lyso1/LCK75r2/LCK75 images/mainboard.png

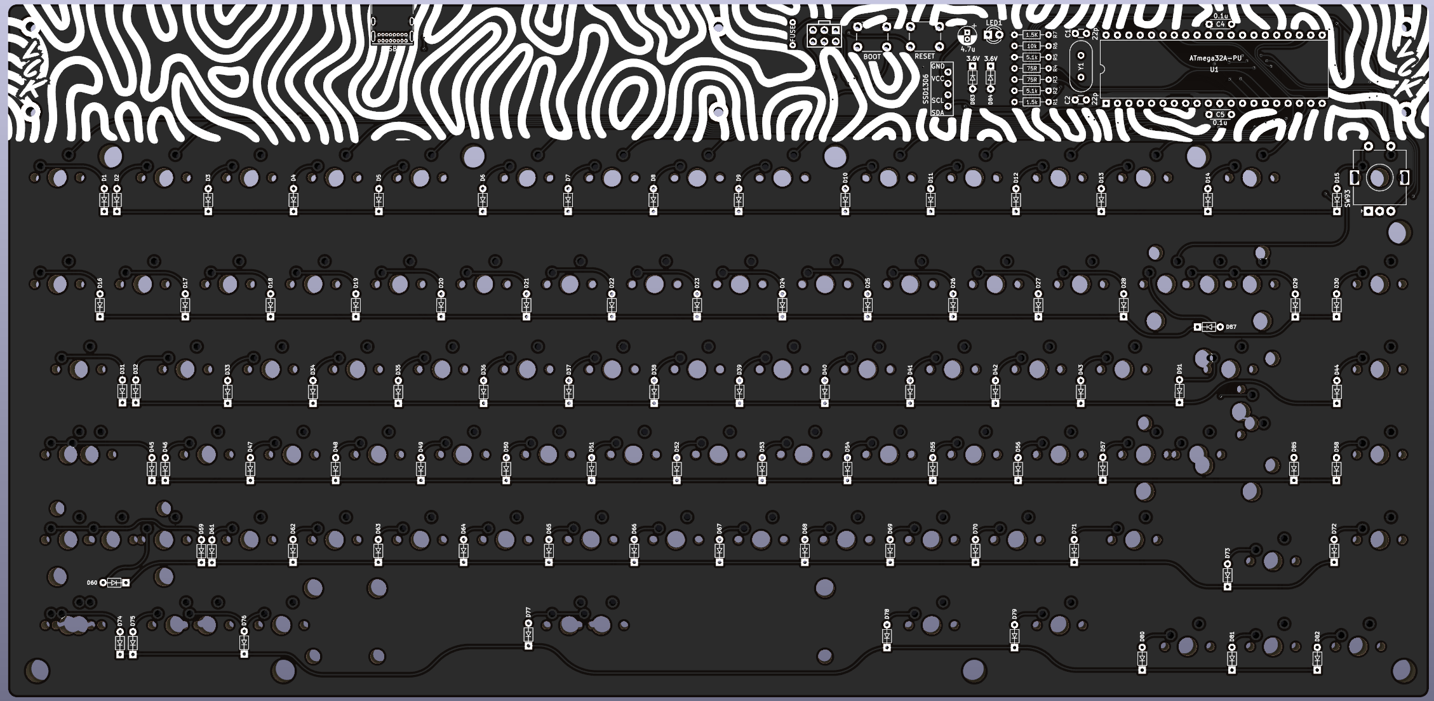
LCK75 images/mainboard.png
