lyso1/LCK75r2/LCK75gerbers&parts/LCK75r2-MAINBOARD/LCK75.kicad_sch

## KiCad design LCK75gerbers&parts/LCK75r2-MAINBOARD/LCK75.kicad_sch (2022-02-10)

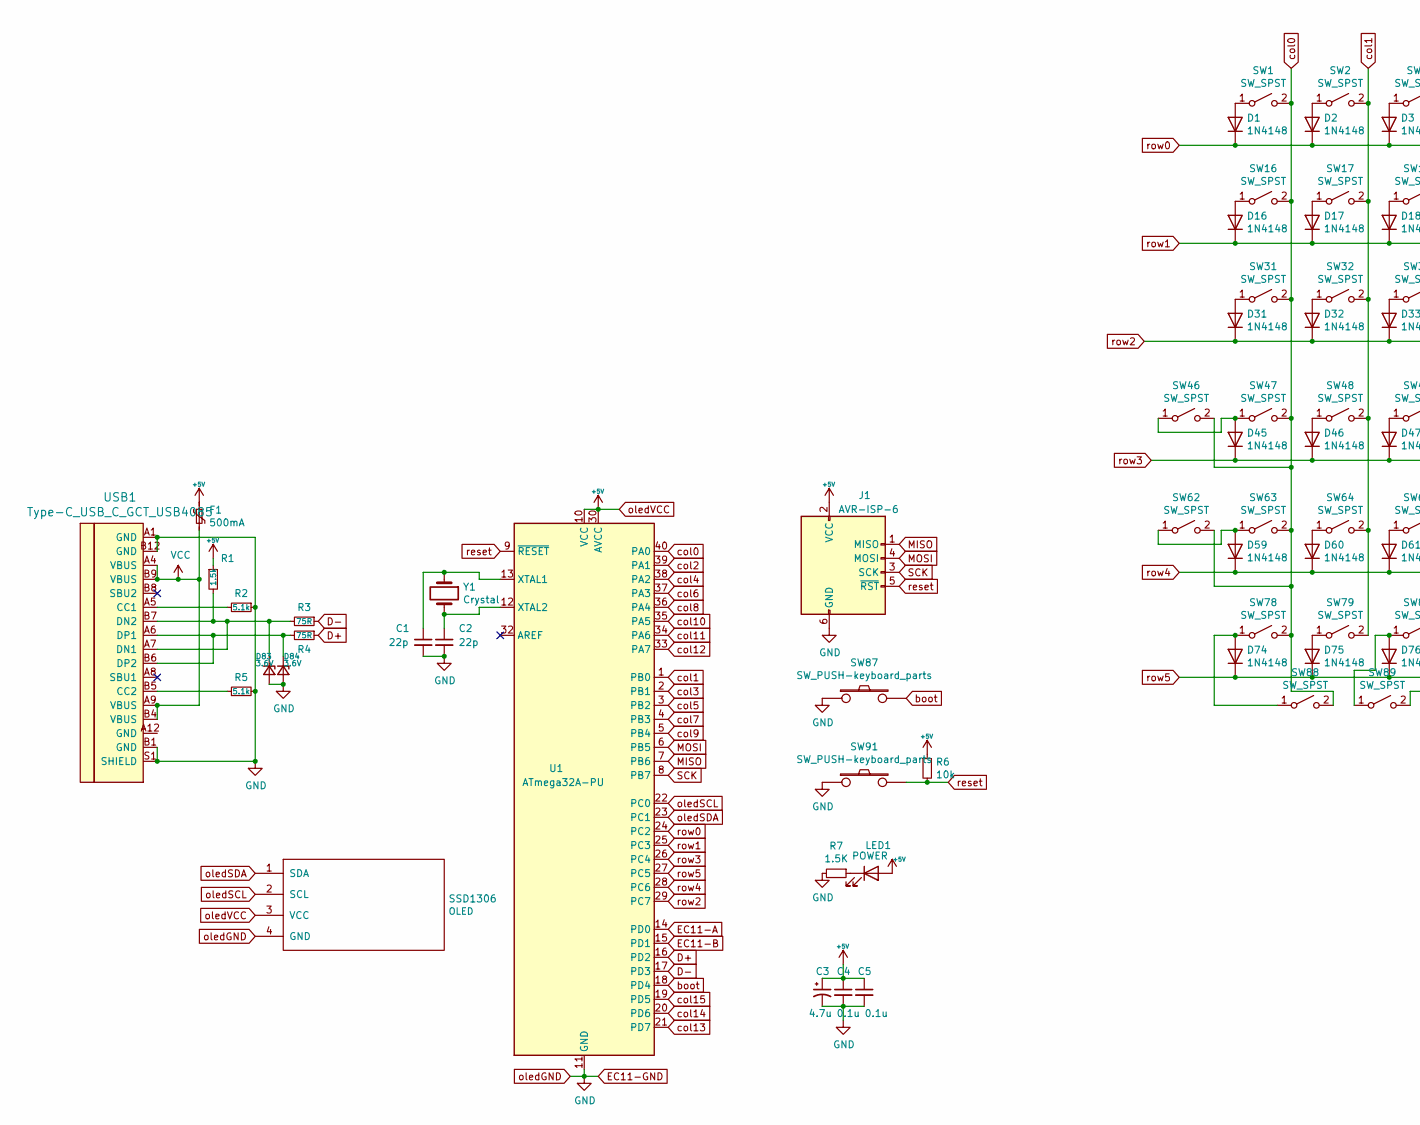
[picture p14: schematic LCK75.kicad_sch, part in row 1, column 1]

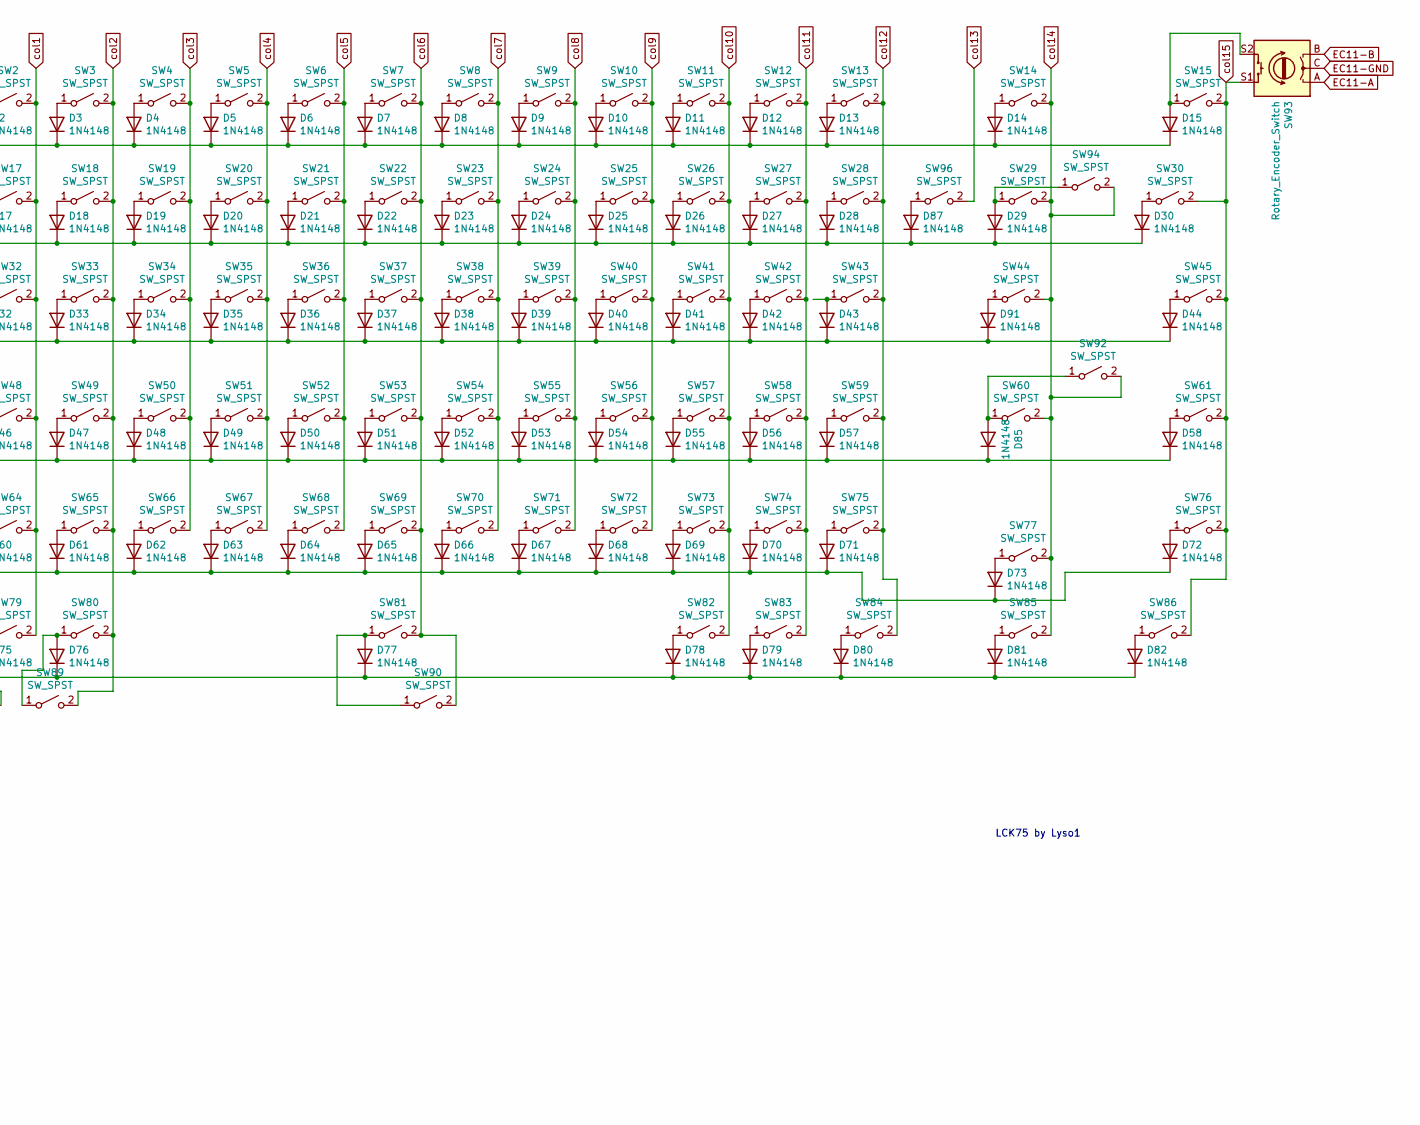
[picture p15: schematic LCK75.kicad_sch, part in row 1, column 2]

Parts:
C1, C2: 22p; C_Disc_D3.0mm_W1.6mm_P2.50mm
C3: 4.7u; CP_Radial_D4.0mm_P1.50mm
C4, C5: 0.1u; C_Disc_D4.3mm_W1.9mm_P5.00mm
D1, D2, D3, D4, D5, D6, D7, D8, D9, D10, D11, D12, D13, D14, D15, D16, D17, D18, D19, D20, D21, D22, D23, D24, D25, D26, D27, D28, D29, D30, D31, D32, D33, D34, D35, D36, D37, D38, D39, D40, D41, D42, D43, D44, D45, D46, D47, D48, D49, D50, D51, D52, D53, D54, D55, D56, D57, D58, D59, D60, D61, D62, D63, D64, D65, D66, D67, D68, D69, D70, D71, D72, D73, D74, D75, D76, D77, D78, D79, D80, D81, D82, D85, D87, D91: 1N4148; D_DO-35_SOD27_P5.08mm_Horizontal
D83, D84: 3.6V; D_DO-35_SOD27_P5.08mm_Horizontal
F1: 500mA; polyfuse_5.1mm
J1: AVR-ISP-6; AVR_ICSP_3x2
LED1: POWER; LED_D3.0mm
R1: 1.5k; R_Axial_DIN0204_L3.6mm_D1.6mm_P7.62mm_Horizontal
R2, R5: 5.1k; R_Axial_DIN0204_L3.6mm_D1.6mm_P7.62mm_Horizontal
R3, R4: 75R; R_Axial_DIN0204_L3.6mm_D1.6mm_P7.62mm_Horizontal
R6: 10k; R_Axial_DIN0204_L3.6mm_D1.6mm_P7.62mm_Horizontal
R7: 1.5K; R_Axial_DIN0204_L3.6mm_D1.6mm_P7.62mm_Horizontal
SSD1306: OLED; ssd1306 128x32 oled
SW1, SW2, SW3, SW4, SW5, SW6, SW7, SW8, SW9, SW10, SW11, SW12, SW13, SW14, SW15, SW16, SW17, SW18, SW19, SW20, SW21, SW22, SW23, SW24, SW25, SW26, SW27, SW28, SW30, SW32, SW33, SW34, SW35, SW36, SW37, SW38, SW39, SW40, SW41, SW42, SW43, SW45, SW46, SW48, SW49, SW50, SW51, SW52, SW53, SW54, SW55, SW56, SW57, SW58, SW59, SW61, SW64, SW65, SW66, SW67, SW68, SW69, SW70, SW71, SW72, SW73, SW74, SW76, SW77, SW84, SW85, SW86, SW94, SW96: SW_SPST; MXOnly-1U-NoLED
SW29: SW_SPST; MXOnly-2U-NoLED
SW31, SW44, SW82, SW83, SW88, SW89: SW_SPST; MXOnly-1.5U-NoLED
SW47, SW75: SW_SPST; MXOnly-1.75U-NoLED
SW60, SW63: SW_SPST; MXOnly-2.25U-NoLED
SW62, SW78, SW79, SW80: SW_SPST; MXOnly-1.25U-NoLED
SW81: SW_SPST; MXOnly-7U-ReversedStabilizers-NoLED
SW87, SW91: SW_PUSH-keyboard_parts; SW_PUSH_6mm
SW90: SW_SPST; MXOnly-6.25U-ReversedStabilizers-NoLED
SW92: SW_SPST; MXOnly-ISO-ROTATED-ReversedStabilizers-NoLED
SW93: Rotary_Encoder_Switch; RotaryEncoder_Alps_EC11E-Switch_Vertical_H20mm-new
U1: ATmega32A-PU; DIP-40_W15.24mm
USB1: Type-C_USB_C_GCT_USB4085; USB_C_Receptacle_GCT_USB4085
Y1: Crystal; Crystal_HC49-4H_Vertical

Connections:
+5V: C3.1, C4.1, C5.1, F1.1, J1.2 (VCC), LED1.2 (A), R1.1, R6.1, SSD1306.3 (VCC), U1.10 (VCC), U1.30 (AVCC)
D+: R4.1, U1.16 (PD2)
D-: R3.1, U1.17 (PD3)
EC11-A: SW93.A, U1.14 (PD0)
EC11-B: SW93.B, U1.15 (PD1)
EC11-GND: C1.2, C2.2, C3.2, C4.2, C5.2, D83.2 (A), D84.2 (A), J1.6 (GND), R2.1, R5.2, R7.2, SSD1306.4 (GND), SW87.1, SW91.1, SW93.C, U1.11 (GND), U1.31 (GND), USB1.A1 (GND), USB1.B1 (GND), USB1.B12 (GND), USB1.S1 (SHIELD)
MISO: J1.1 (MISO), U1.7 (PB6)
MOSI: J1.4 (MOSI), U1.6 (PB5)
unnamed: C1.1, U1.13 (XTAL1), Y1.1
unnamed: C2.1, U1.12 (XTAL2), Y1.2
unnamed: D1.2 (A), SW1.1 (A)
unnamed: D2.2 (A), SW2.1 (A)
unnamed: D3.2 (A), SW3.1 (A)
unnamed: D4.2 (A), SW4.1 (A)
unnamed: D5.2 (A), SW5.1 (A)
unnamed: D6.2 (A), SW6.1 (A)
unnamed: D7.2 (A), SW7.1 (A)
unnamed: D8.2 (A), SW8.1 (A)
unnamed: D9.2 (A), SW9.1 (A)
unnamed: D10.2 (A), SW10.1 (A)
unnamed: D11.2 (A), SW11.1 (A)
unnamed: D12.2 (A), SW12.1 (A)
unnamed: D13.2 (A), SW13.1 (A)
unnamed: D14.2 (A), SW14.1 (A)
unnamed: D15.2 (A), SW15.1 (A), SW93.S2
unnamed: D16.2 (A), SW16.1 (A)
unnamed: D17.2 (A), SW17.1 (A)
unnamed: D18.2 (A), SW18.1 (A)
unnamed: D19.2 (A), SW19.1 (A)
unnamed: D20.2 (A), SW20.1 (A)
unnamed: D21.2 (A), SW21.1 (A)
unnamed: D22.2 (A), SW22.1 (A)
unnamed: D23.2 (A), SW23.1 (A)
unnamed: D24.2 (A), SW24.1 (A)
unnamed: D25.2 (A), SW25.1 (A)
unnamed: D26.2 (A), SW26.1 (A)
unnamed: D27.2 (A), SW27.1 (A)
unnamed: D28.2 (A), SW28.1 (A)
unnamed: D29.2 (A), SW29.1 (A), SW94.1 (A)
unnamed: D30.2 (A), SW30.1 (A)
unnamed: D31.2 (A), SW31.1 (A)
unnamed: D32.2 (A), SW32.1 (A)
unnamed: D33.2 (A), SW33.1 (A)
unnamed: D34.2 (A), SW34.1 (A)
unnamed: D35.2 (A), SW35.1 (A)
unnamed: D36.2 (A), SW36.1 (A)
unnamed: D37.2 (A), SW37.1 (A)
unnamed: D38.2 (A), SW38.1 (A)
unnamed: D39.2 (A), SW39.1 (A)
unnamed: D40.2 (A), SW40.1 (A)
unnamed: D41.2 (A), SW41.1 (A)
unnamed: D42.2 (A), SW42.1 (A)
unnamed: D43.2 (A), SW43.1 (A)
unnamed: D44.2 (A), SW45.1 (A)
unnamed: D45.2 (A), SW46.1 (A), SW47.1 (A)
unnamed: D46.2 (A), SW48.1 (A)
unnamed: D47.2 (A), SW49.1 (A)
unnamed: D48.2 (A), SW50.1 (A)
unnamed: D49.2 (A), SW51.1 (A)
unnamed: D50.2 (A), SW52.1 (A)
unnamed: D51.2 (A), SW53.1 (A)
unnamed: D52.2 (A), SW54.1 (A)
unnamed: D53.2 (A), SW55.1 (A)
unnamed: D54.2 (A), SW56.1 (A)
unnamed: D55.2 (A), SW57.1 (A)
unnamed: D56.2 (A), SW58.1 (A)
unnamed: D57.2 (A), SW59.1 (A)
unnamed: D58.2 (A), SW61.1 (A)
unnamed: D59.2 (A), SW62.1 (A), SW63.1 (A)
unnamed: D60.2 (A), SW64.1 (A)
unnamed: D61.2 (A), SW65.1 (A)
unnamed: D62.2 (A), SW66.1 (A)
unnamed: D63.2 (A), SW67.1 (A)
unnamed: D64.2 (A), SW68.1 (A)
unnamed: D65.2 (A), SW69.1 (A)
unnamed: D66.2 (A), SW70.1 (A)
unnamed: D67.2 (A), SW71.1 (A)
unnamed: D68.2 (A), SW72.1 (A)
unnamed: D69.2 (A), SW73.1 (A)
unnamed: D70.2 (A), SW74.1 (A)
unnamed: D71.2 (A), SW75.1 (A)
unnamed: D72.2 (A), SW76.1 (A)
unnamed: D73.2 (A), SW77.1 (A)
unnamed: D74.2 (A), SW78.1 (A), SW88.1 (A)
unnamed: D75.2 (A), SW79.1 (A)
unnamed: D76.2 (A), SW80.1 (A), SW89.1 (A)
unnamed: D77.2 (A), SW81.1 (A), SW90.1 (A)
unnamed: D78.2 (A), SW82.1 (A)
unnamed: D79.2 (A), SW83.1 (A)
unnamed: D80.2 (A), SW84.1 (A)
unnamed: D81.2 (A), SW85.1 (A)
unnamed: D82.2 (A), SW86.1 (A)
unnamed: D83.1 (K), R1.2, R3.2, USB1.A7 (DN1), USB1.B7 (DN2)
unnamed: D84.1 (K), R4.2, USB1.A6 (DP1), USB1.B6 (DP2)
unnamed: D85.2 (A), SW60.1 (A), SW92.1 (A)
unnamed: D87.2 (A), SW96.1 (A)
unnamed: D91.2 (A), SW44.1 (A)
unnamed: LED1.1 (K), R7.1
unnamed: R2.2, USB1.A5 (CC1)
unnamed: R5.1, USB1.B5 (CC2)
SCK: J1.3 (SCK), U1.8 (PB7)
VCC: F1.2, USB1.A4 (VBUS), USB1.A9 (VBUS), USB1.B4 (VBUS), USB1.B9 (VBUS)
boot: SW87.2, U1.18 (PD4)
col0: SW1.2 (B), SW16.2 (B), SW31.2 (B), SW46.2 (B), SW47.2 (B), SW62.2 (B), SW63.2 (B), SW78.2 (B), SW88.2 (B), U1.40 (PA0)
col1: SW2.2 (B), SW17.2 (B), SW32.2 (B), SW48.2 (B), SW64.2 (B), SW79.2 (B), U1.1 (PB0)
col2: SW3.2 (B), SW18.2 (B), SW33.2 (B), SW49.2 (B), SW65.2 (B), SW80.2 (B), SW89.2 (B), U1.39 (PA1)
col3: SW4.2 (B), SW19.2 (B), SW34.2 (B), SW50.2 (B), SW66.2 (B), U1.2 (PB1)
col4: SW5.2 (B), SW20.2 (B), SW35.2 (B), SW51.2 (B), SW67.2 (B), U1.38 (PA2)
col5: SW6.2 (B), SW21.2 (B), SW36.2 (B), SW52.2 (B), SW68.2 (B), U1.3 (PB2)
col6: SW7.2 (B), SW22.2 (B), SW37.2 (B), SW53.2 (B), SW69.2 (B), SW81.2 (B), SW90.2 (B), U1.37 (PA3)
col7: SW8.2 (B), SW23.2 (B), SW38.2 (B), SW54.2 (B), SW70.2 (B), U1.4 (PB3)
col8: SW9.2 (B), SW24.2 (B), SW39.2 (B), SW55.2 (B), SW71.2 (B), U1.36 (PA4)
col9: SW10.2 (B), SW25.2 (B), SW40.2 (B), SW56.2 (B), SW72.2 (B), U1.5 (PB4)
col10: SW11.2 (B), SW26.2 (B), SW41.2 (B), SW57.2 (B), SW73.2 (B), SW82.2 (B), U1.35 (PA5)
col11: SW12.2 (B), SW27.2 (B), SW42.2 (B), SW58.2 (B), SW74.2 (B), SW83.2 (B), U1.34 (PA6)
col12: SW13.2 (B), SW28.2 (B), SW43.2 (B), SW59.2 (B), SW75.2 (B), SW84.2 (B), U1.33 (PA7)
col13: SW96.2 (B), U1.21 (PD7)
col14: SW14.2 (B), SW29.2 (B), SW44.2 (B), SW60.2 (B), SW77.2 (B), SW85.2 (B), SW92.2 (B), SW94.2 (B), U1.20 (PD6)
col15: SW15.2 (B), SW30.2 (B), SW45.2 (B), SW61.2 (B), SW76.2 (B), SW86.2 (B), SW93.S1, U1.19 (PD5)
oledSCL: SSD1306.2 (SCL), U1.22 (PC0)
oledSDA: SSD1306.1 (SDA), U1.23 (PC1)
reset: J1.5 (~RST), R6.2, SW91.2, U1.9 (~RESET)
row0: D1.1 (K), D2.1 (K), D3.1 (K), D4.1 (K), D5.1 (K), D6.1 (K), D7.1 (K), D8.1 (K), D9.1 (K), D10.1 (K), D11.1 (K), D12.1 (K), D13.1 (K), D14.1 (K), D15.1 (K), U1.24 (PC2)
row1: D16.1 (K), D17.1 (K), D18.1 (K), D19.1 (K), D20.1 (K), D21.1 (K), D22.1 (K), D23.1 (K), D24.1 (K), D25.1 (K), D26.1 (K), D27.1 (K), D28.1 (K), D29.1 (K), D30.1 (K), D87.1 (K), U1.25 (PC3)
row2: D31.1 (K), D32.1 (K), D33.1 (K), D34.1 (K), D35.1 (K), D36.1 (K), D37.1 (K), D38.1 (K), D39.1 (K), D40.1 (K), D41.1 (K), D42.1 (K), D43.1 (K), D44.1 (K), D91.1 (K), U1.29 (PC7)
row3: D45.1 (K), D46.1 (K), D47.1 (K), D48.1 (K), D49.1 (K), D50.1 (K), D51.1 (K), D52.1 (K), D53.1 (K), D54.1 (K), D55.1 (K), D56.1 (K), D57.1 (K), D58.1 (K), D85.1 (K), U1.26 (PC4)
row4: D59.1 (K), D60.1 (K), D61.1 (K), D62.1 (K), D63.1 (K), D64.1 (K), D65.1 (K), D66.1 (K), D67.1 (K), D68.1 (K), D69.1 (K), D70.1 (K), D71.1 (K), D72.1 (K), D73.1 (K), U1.28 (PC6)
row5: D74.1 (K), D75.1 (K), D76.1 (K), D77.1 (K), D78.1 (K), D79.1 (K), D80.1 (K), D81.1 (K), D82.1 (K), U1.27 (PC5)

Notes on the sheet:
LCK75 by Lyso1
